XianmingFeng/one-man-432mhz-eme-array/CAD/3d_print/feed_box/feed_box_front.step

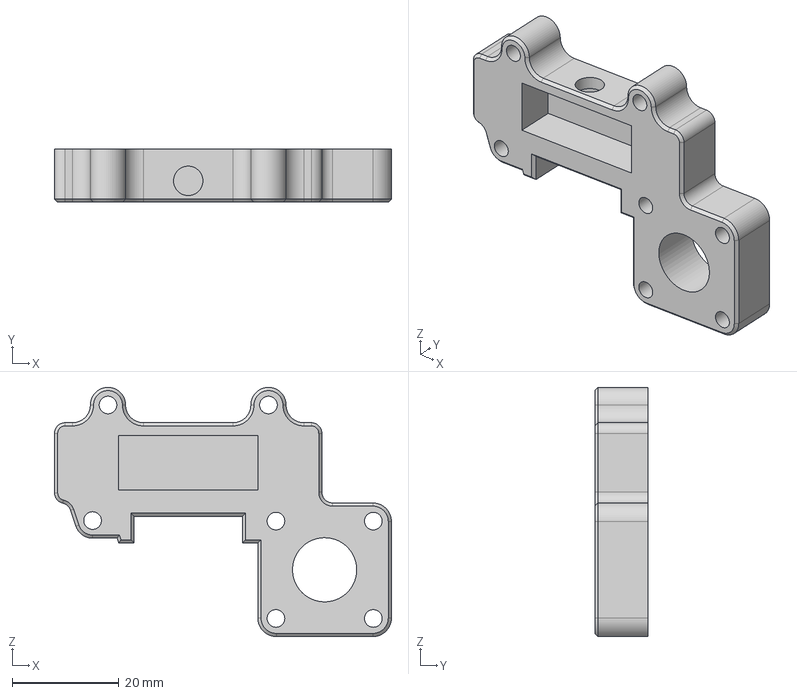
[picture p16: CAD file, 2025-10-26]
CAD/3d_print/feed_box/feed_box_front.step
63.0 x 10.0 x 46.6 mm
