XianmingFeng/one-man-432mhz-eme-array/CAD/aluminum_pipe/yagi_boom_middle.step

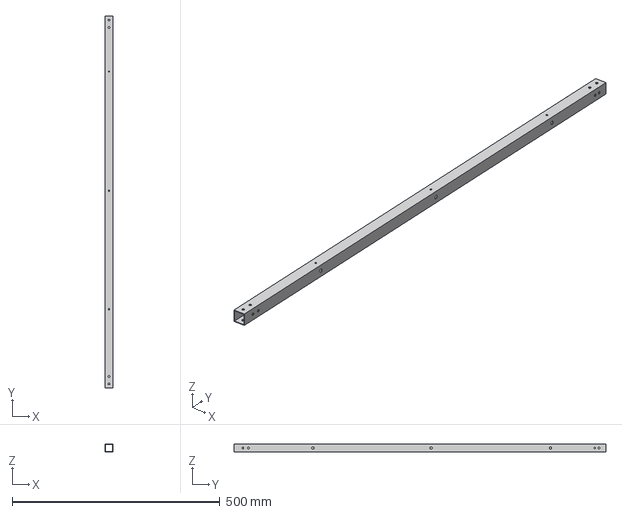
[picture p17: CAD file, 2025-10-26]
CAD/aluminum_pipe/yagi_boom_middle.step
20.0 x 895.0 x 20.0 mm
