XianmingFeng/one-man-432mhz-eme-array/CAD/aluminum_pipe/yagi_boom_front.step

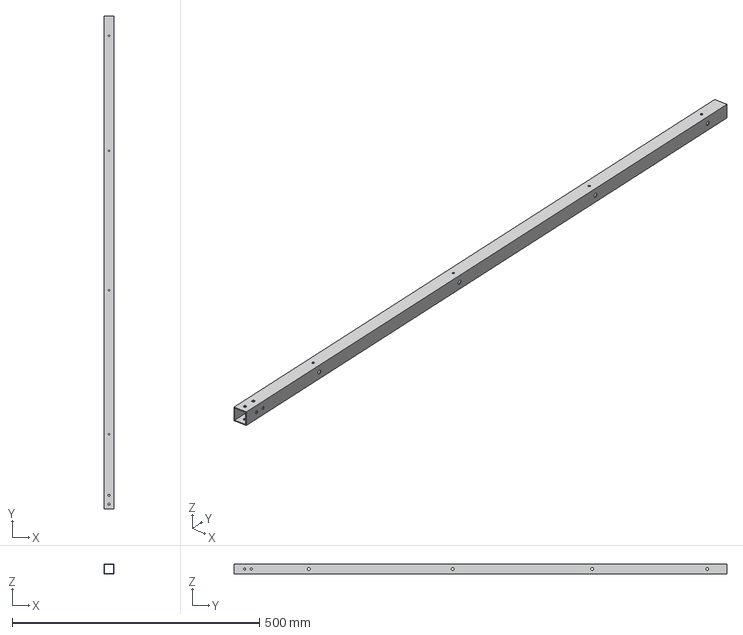
[picture p18: CAD file, 2025-10-26]
CAD/aluminum_pipe/yagi_boom_front.step
20.0 x 997.5 x 20.0 mm
